UWA-Robotics-Club/keyboard-urc75/Build_Instructions/2_Diodes_Img/Solder the Diodes/14.JPG

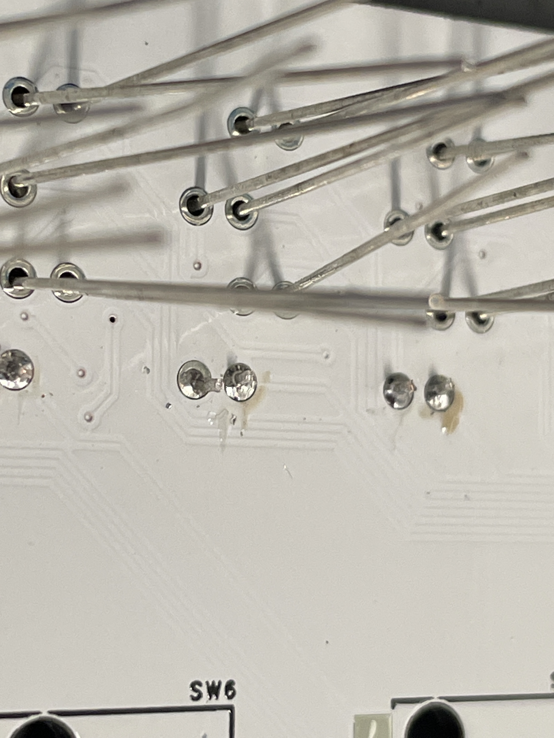
Build_Instructions/2_Diodes_Img/Solder the Diodes/14.JPG
