UWA-Robotics-Club/keyboard-urc75/Build_Instructions/2_Diodes_Img/Thread_Diodes_Through/26.JPG

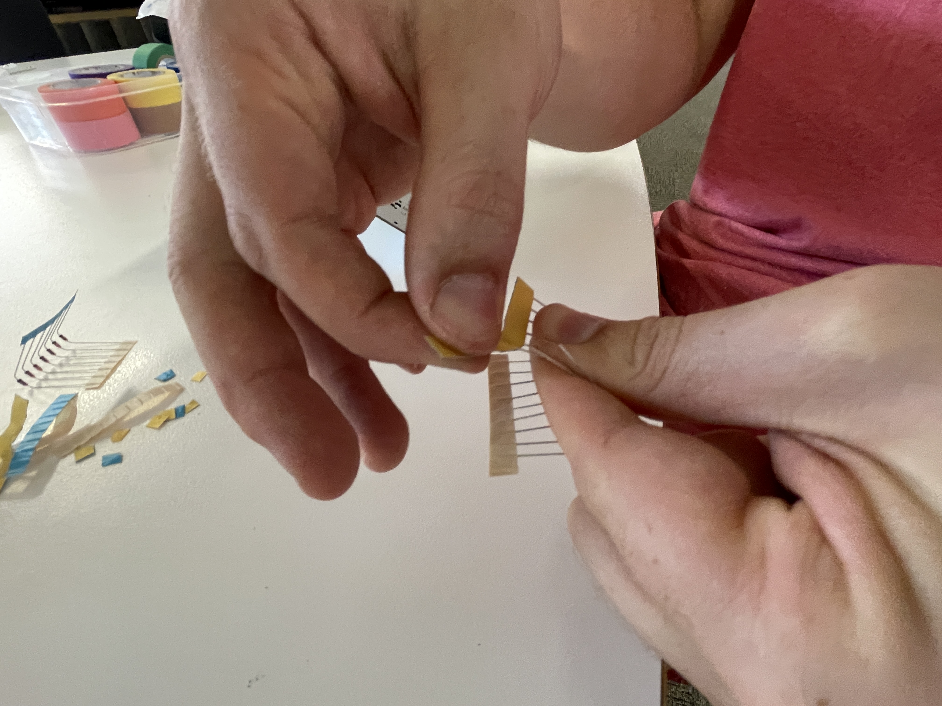
Build_Instructions/2_Diodes_Img/Thread_Diodes_Through/26.JPG
