UWA-Robotics-Club/keyboard-urc75/Build_Instructions/3_Sockets_img/Ready the Scokets/4.JPG

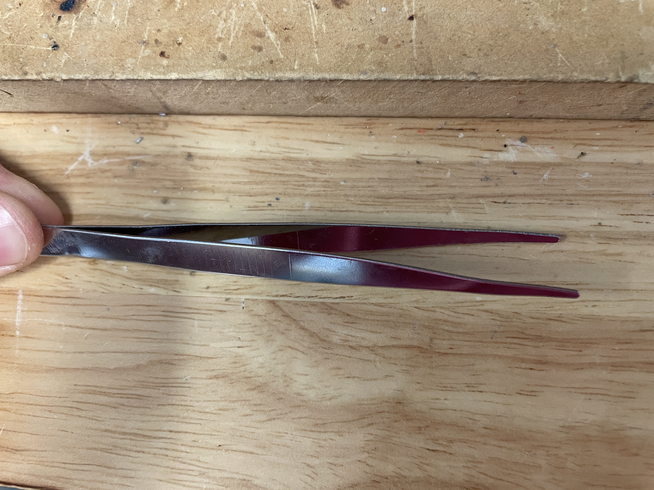
Build_Instructions/3_Sockets_img/Ready the Scokets/4.JPG
