UWA-Robotics-Club/keyboard-urc75/Build_Instructions/3_Sockets_img/Solder the Sockets/6.JPG

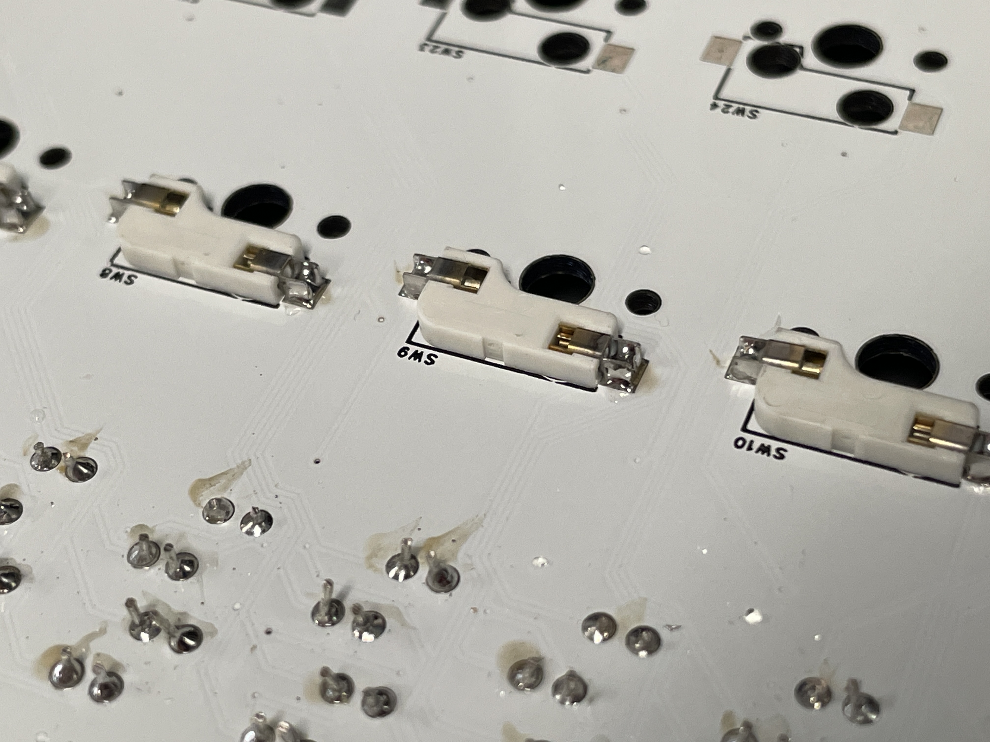
Build_Instructions/3_Sockets_img/Solder the Sockets/6.JPG
