UWA-Robotics-Club/keyboard-urc75/Build_Instructions/4_OLED_img/Solder the OLED/8.JPG

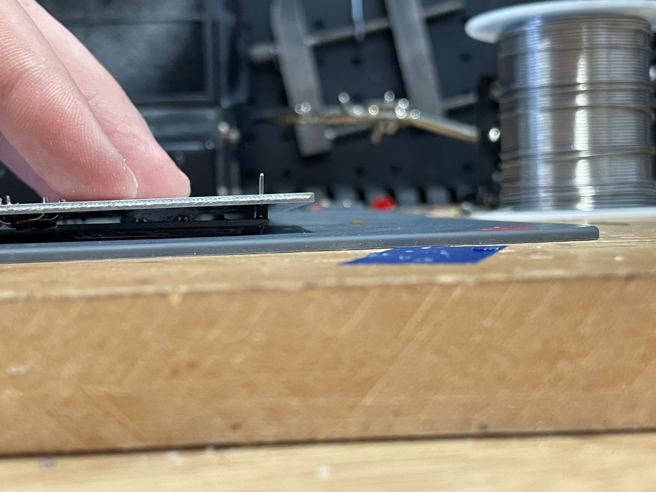
Build_Instructions/4_OLED_img/Solder the OLED/8.JPG
