UWA-Robotics-Club/keyboard-urc75/Build_Instructions/6_Heatsets_Case_img/Add the Stabilisers/3.JPG

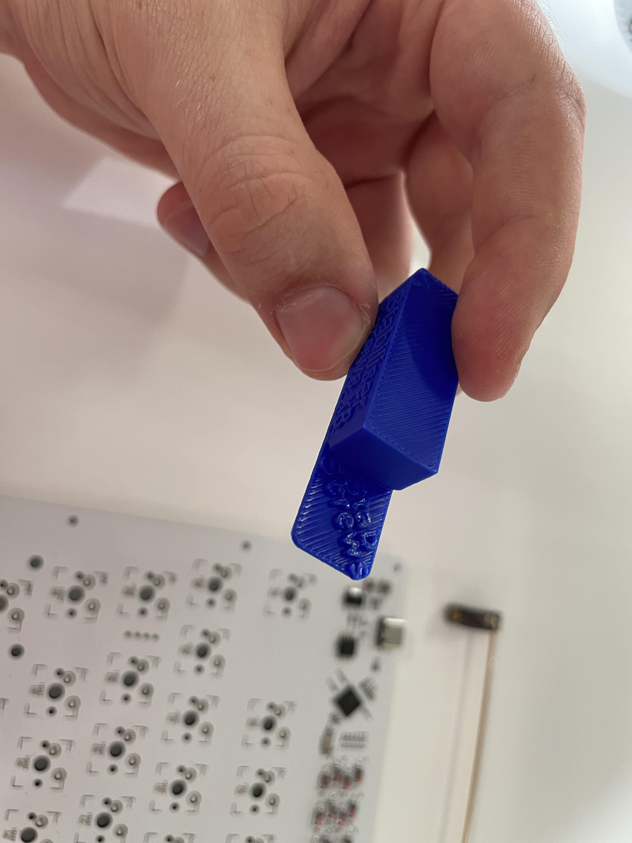
Build_Instructions/6_Heatsets_Case_img/Add the Stabilisers/3.JPG
