UWA-Robotics-Club/keyboard-urc75/Build_Instructions/6_Heatsets_Case_img/Add_Heatsets_to_Case/15.JPG

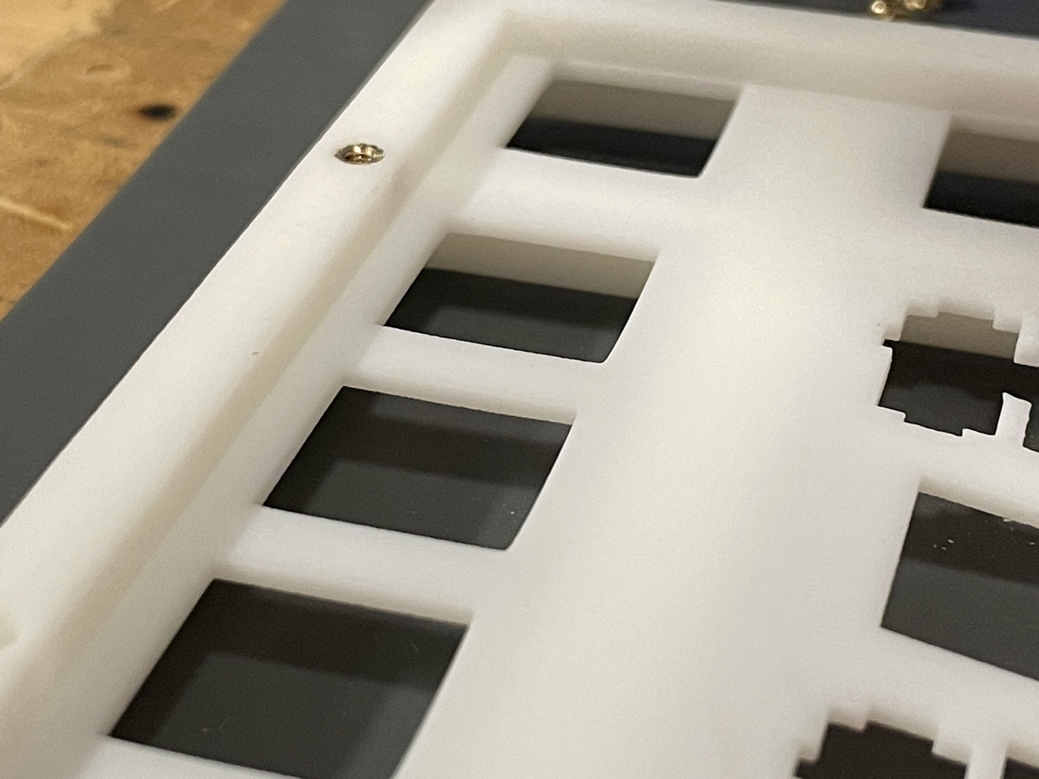
Build_Instructions/6_Heatsets_Case_img/Add_Heatsets_to_Case/15.JPG
