UWA-Robotics-Club/keyboard-urc75/Build_Instructions/6_Heatsets_Case_img/Screw PCB to Bottom Case/8.JPG

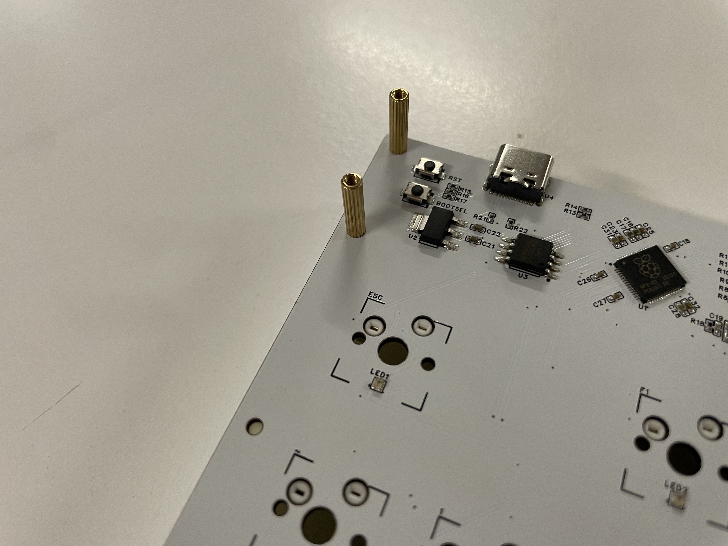
Build_Instructions/6_Heatsets_Case_img/Screw PCB to Bottom Case/8.JPG
