UWA-Robotics-Club/keyboard-urc75/Build_Instructions/5_Testing_Solder_Joints_img/Flash the Firmware to Test the LEDS/2.JPG

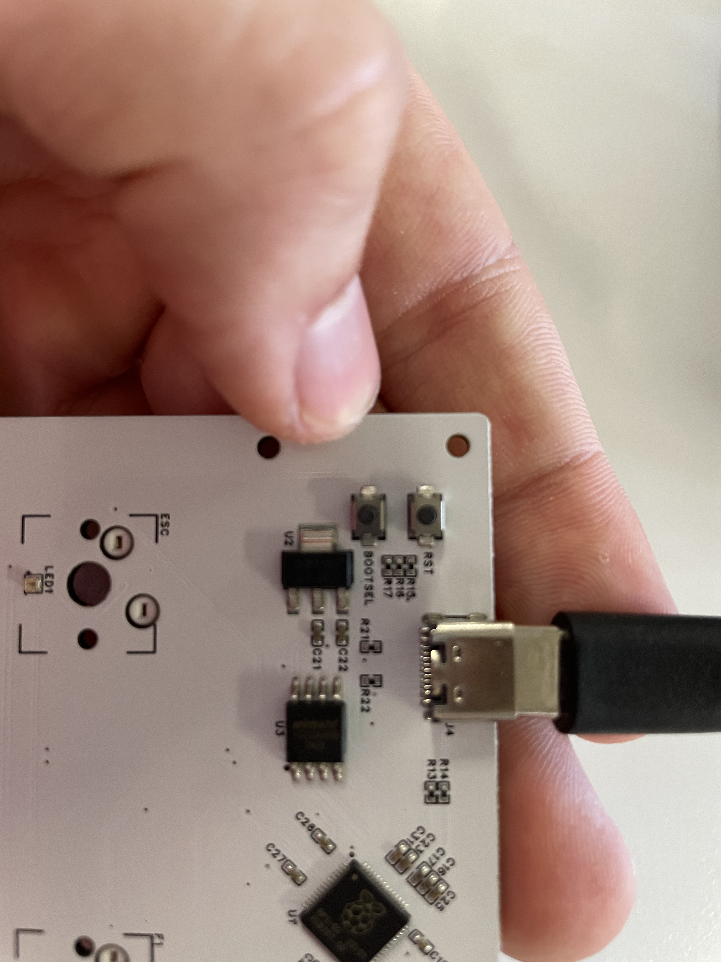
Build_Instructions/5_Testing_Solder_Joints_img/Flash the Firmware to Test the LEDS/2.JPG
