UWA-Robotics-Club/keyboard-urc75/Build_Instructions/6_Heatsets_Case_img/Add Top Case and Screw from bottom/17.JPG

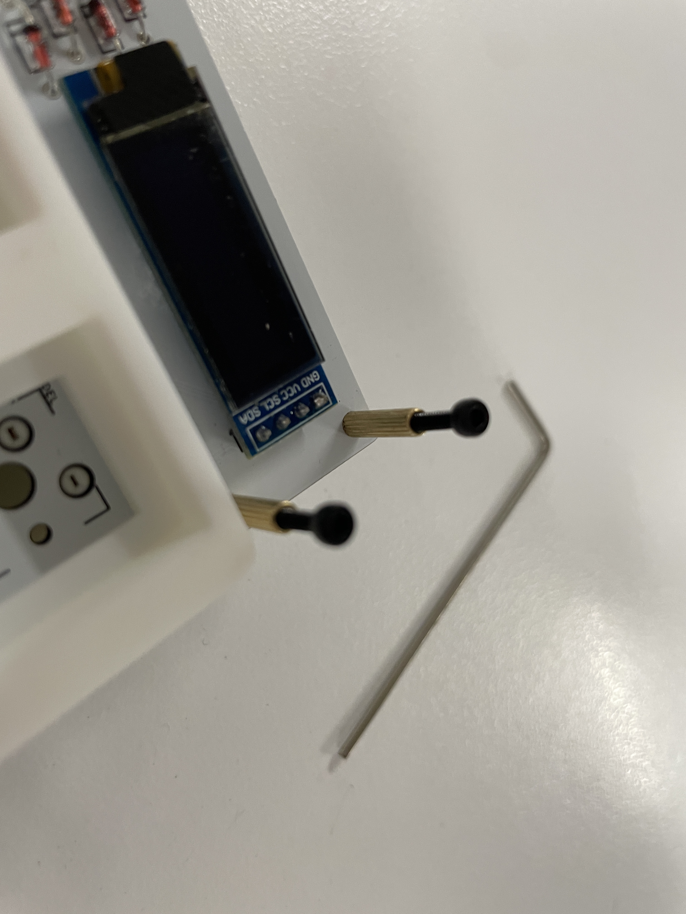
Build_Instructions/6_Heatsets_Case_img/Add Top Case and Screw from bottom/17.JPG
